pato/LEDStatusIndicator/PCB/render/large_i2.png

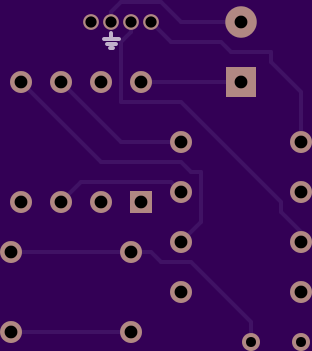
PCB/render/large_i2.png
