pato/LEDStatusIndicator/PCB/render/large_i3.png

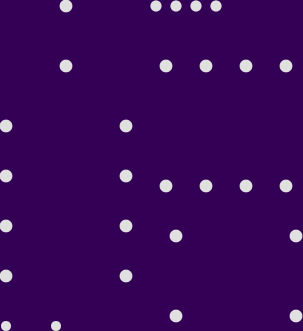
PCB/render/large_i3.png
