pato/LEDStatusIndicator/PCB/render/large_i.png

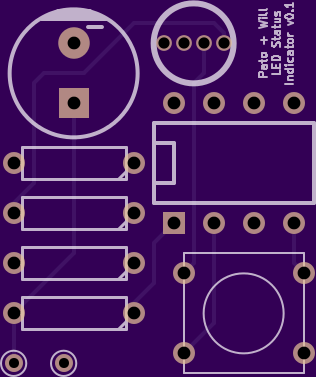
PCB/render/large_i.png
